damianbubak92/bramka-setup/Shared/KiCadLib/3dmodels/KEY-SMD_4P-L6.0-W6.0-P4.50-LS10.0.step

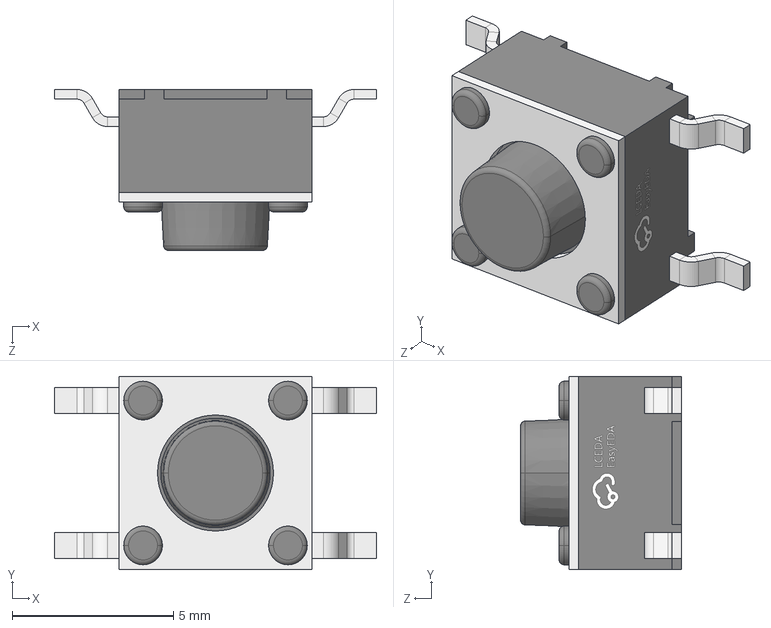
[picture p16: CAD file, 2026-07-04]
Shared/KiCadLib/3dmodels/KEY-SMD_4P-L6.0-W6.0-P4.50-LS10.0.step
10.0 x 6.00 x 5.00 mm
