damianbubak92/bramka-setup/Shared/KiCadLib/3dmodels/WSON-10_L2.5-W2.5-W0.50-TL-EP.step

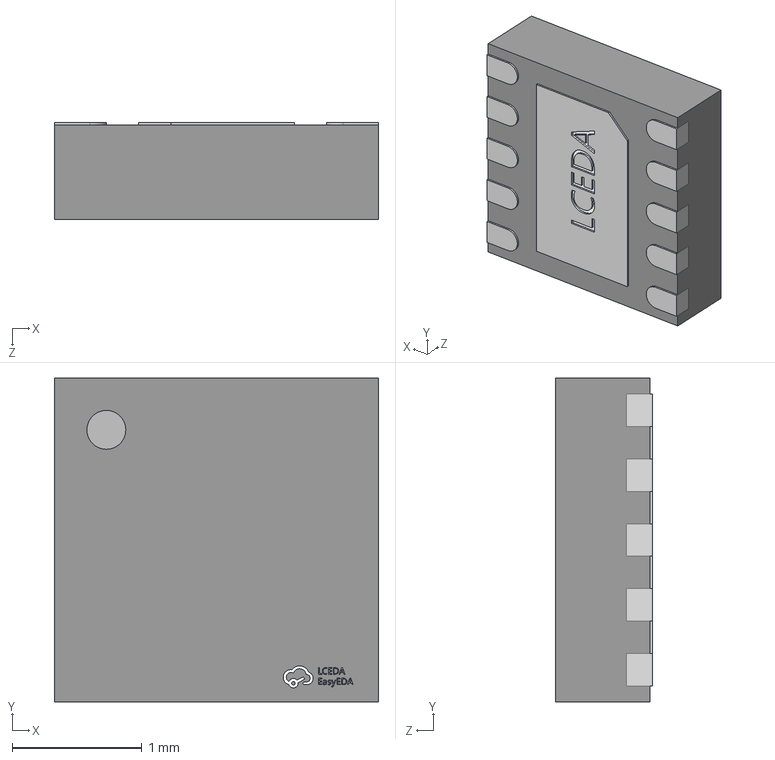
[picture p17: CAD file, 2026-07-04]
Shared/KiCadLib/3dmodels/WSON-10_L2.5-W2.5-W0.50-TL-EP.step
2.50 x 2.50 x 0.751 mm
