damianbubak92/bramka-setup/Shared/KiCadLib/3dmodels/SOT-23-6_L2.9-W1.6-H1.5-LS2.8-P0.95.step

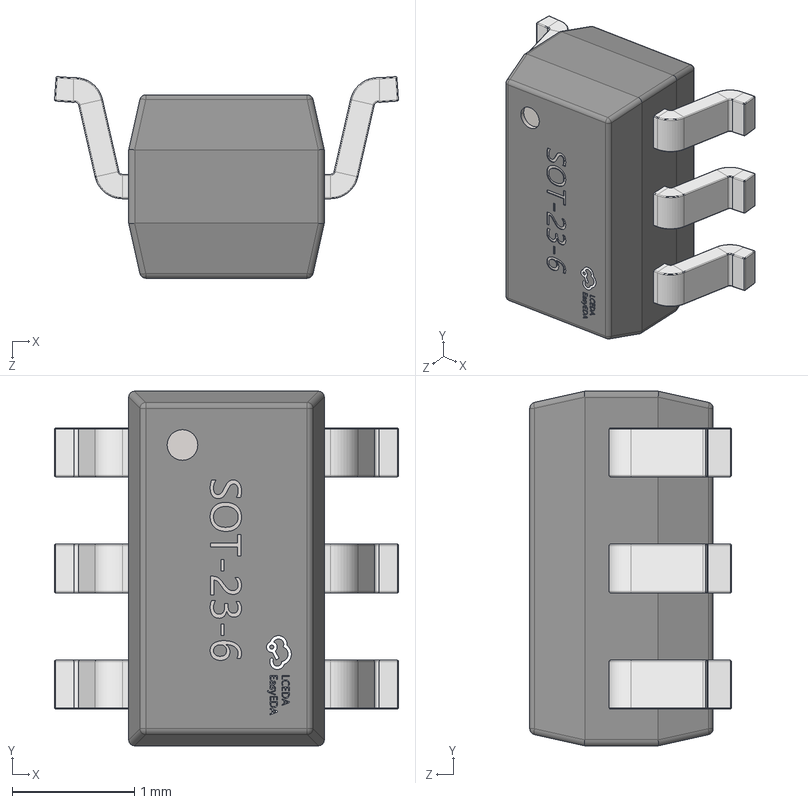
[picture p18: CAD file, 2026-07-04]
Shared/KiCadLib/3dmodels/SOT-23-6_L2.9-W1.6-H1.5-LS2.8-P0.95.step
2.81 x 2.90 x 1.65 mm
