damianbubak92/bramka-setup/Shared/KiCadLib/3dmodels/DFN-8_L2.5-W2.5-H1.0-P0.50.step

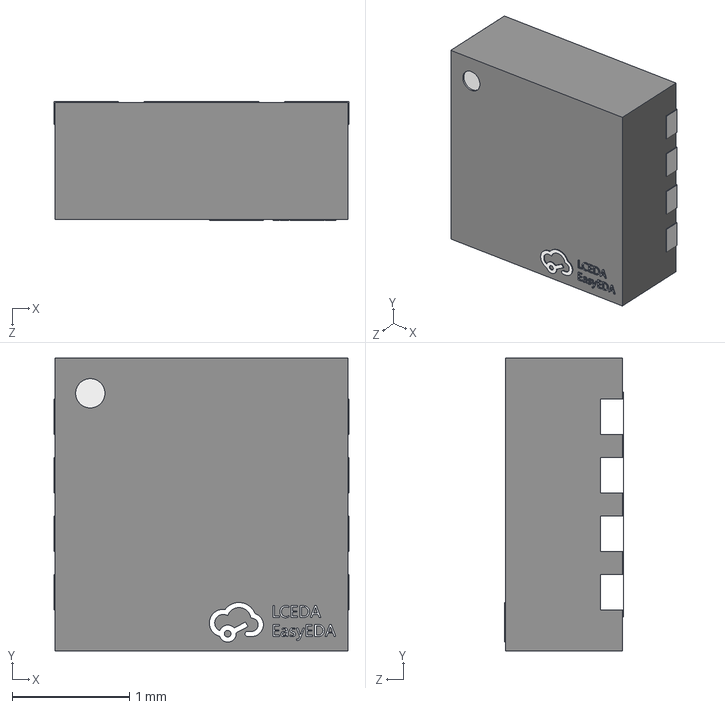
[picture p19: CAD file, 2026-07-03]
Shared/KiCadLib/3dmodels/DFN-8_L2.5-W2.5-H1.0-P0.50.step
2.52 x 2.50 x 1.02 mm
