damianbubak92/bramka-setup/Shared/KiCadLib/3dmodels/CC1310F128RGZR.step

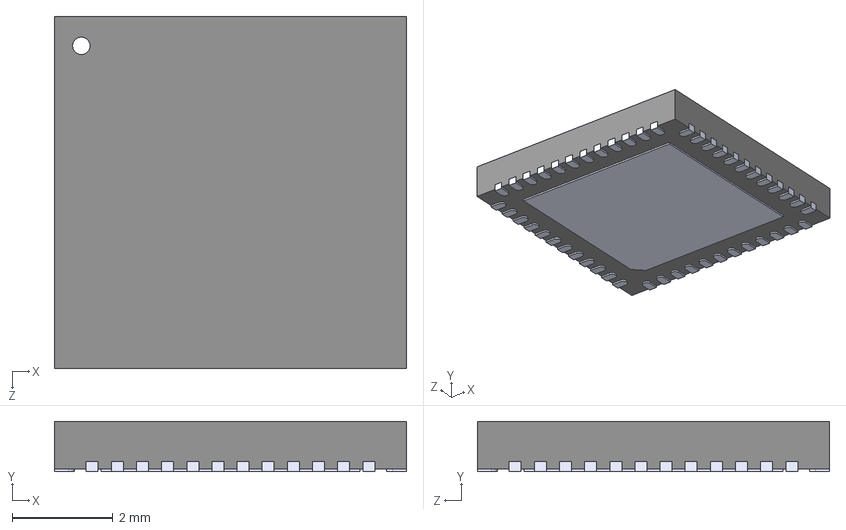
[picture p20: CAD file, 2026-07-03]
Shared/KiCadLib/3dmodels/CC1310F128RGZR.step
7.00 x 1.00 x 7.00 mm
