damianbubak92/bramka-setup/Shared/KiCadLib/3dmodels/DFN-10_L3.0-W3.0-H0.9-P0.50.step

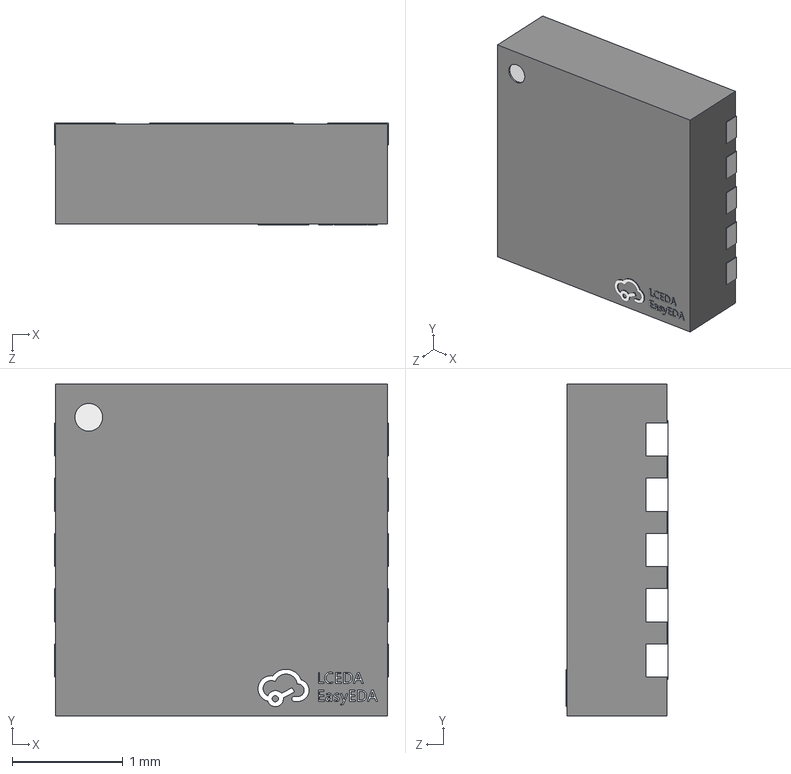
[picture p21: CAD file, 2026-07-03]
Shared/KiCadLib/3dmodels/DFN-10_L3.0-W3.0-H0.9-P0.50.step
3.02 x 3.00 x 0.92 mm
