damianbubak92/bramka-setup/Shared/KiCadLib/3dmodels/USB-C-SMD_TYPE-C-6PIN-2MD-073.step

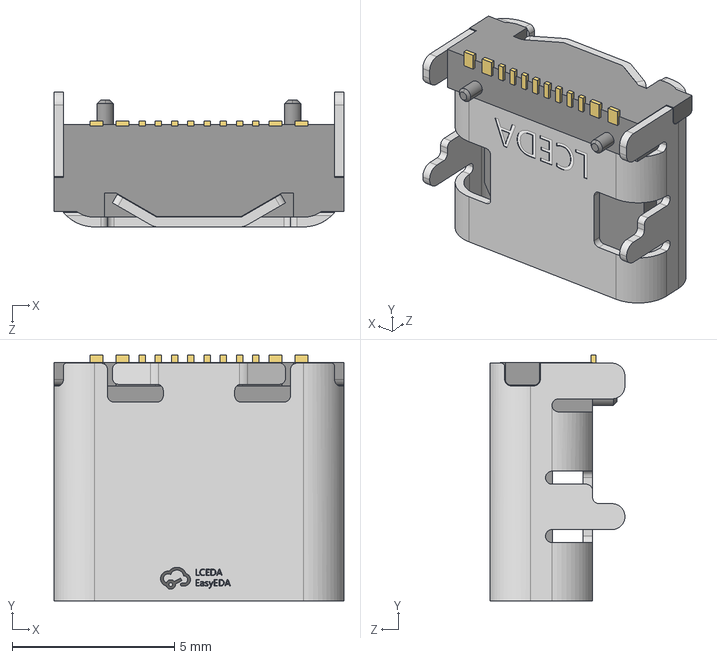
[picture p22: CAD file, 2026-07-03]
Shared/KiCadLib/3dmodels/USB-C-SMD_TYPE-C-6PIN-2MD-073.step
8.94 x 7.58 x 4.16 mm
