damianbubak92/bramka-setup/Nodes/LightSwitchNode/Firmware/scif.c

/// \addtogroup module_scif_driver_setup
//@{
#include "scif.h"
#include "scif_framework.h"
#include <ti/devices/DeviceFamily.h>
#include DeviceFamily_constructPath(inc/hw_types.h)
#include DeviceFamily_constructPath(inc/hw_memmap.h)
#include DeviceFamily_constructPath(inc/hw_aon_event.h)
#include DeviceFamily_constructPath(inc/hw_aon_rtc.h)
#include DeviceFamily_constructPath(inc/hw_aon_pmctl.h)
#include DeviceFamily_constructPath(inc/hw_aux_sce.h)
#include DeviceFamily_constructPath(inc/hw_aux_smph.h)
#include DeviceFamily_constructPath(inc/hw_aux_spim.h)
#include DeviceFamily_constructPath(inc/hw_aux_evctl.h)
#include DeviceFamily_constructPath(inc/hw_aux_aiodio.h)
#include DeviceFamily_constructPath(inc/hw_aux_timer01.h)
#include DeviceFamily_constructPath(inc/hw_aux_sysif.h)
#include DeviceFamily_constructPath(inc/hw_event.h)
#include DeviceFamily_constructPath(inc/hw_ints.h)
#include DeviceFamily_constructPath(inc/hw_ioc.h)
#include <string.h>
#if defined(__IAR_SYSTEMS_ICC__)
    #include <intrinsics.h>
#endif


// OSAL function prototypes
uint32_t scifOsalEnterCriticalSection(void);
void scifOsalLeaveCriticalSection(uint32_t key);




/// Firmware image to be uploaded to the AUX RAM
static const uint16_t pAuxRamImage[] = {
    /*0x0000*/ 0x140E, 0x0417, 0x140E, 0x0440, 0x140E, 0x044A, 0x140E, 0x0467, 0x140E, 0x0470, 0x140E, 0x0479, 0x140E, 0x0482, 0x8953, 0x9954, 
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
    /*0x03C0*/ 0x9D1E, 0xDDA9, 0x9D25, 0x9DA9, 0x50F1, 0x9F3D, 0x191C, 0x9A08, 0xA60D, 0x1103, 0x9F19, 0x9801, 0x5103, 0x9F3D, 0x10ED, 0xCF39, 
    /*0x03E0*/ 0x9D44, 0xCDAD, 0x9D24, 0x40EF, 0x9F3C, 0x0677, 0x10ED, 0x9F19, 0x50EF, 0xDF1D, 0x6117, 0xEF1E, 0xEA00, 0xBE1F, 0x60F1, 0xEF1E, 
    /*0x0400*/ 0x7103, 0xFF1F, 0xFA60, 0x9E18, 0xED29, 0xA607, 0xFD41, 0xFDA1, 0xFD19, 0xFD26, 0x9D47, 0x9DA9, 0x0615, 0xFD41, 0xFDA1, 0x9DAA, 
    /*0x0420*/ 0xFD19, 0xEDAA, 0xFD26, 0x9D47, 0x9DA9, 0x60ED, 0x9F3E, 0x6103, 0xEF1E, 0xE8E0, 0x7103, 0xEF3F, 0x0626, 0xED45, 0xEDA1, 0xDDAB, 
    /*0x0440*/ 0xED1D, 0xDD44, 0xDDAB, 0xED25, 0xDD46, 0xDDA9, 0x68BF, 0xE802, 0x9F3E, 0xED41, 0xFD41, 0xFDAD, 0xED27, 0xDD2E, 0xA601, 0xDD46, 
    /*0x0460*/ 0xED41, 0xFD41, 0xFDAA, 0xED27, 0xDD2E, 0x9E01, 0xDD46, 0x60EF, 0xDF3E, 0x68BF, 0xE804, 0xDF3E, 0x5117, 0xDF1D, 0xDA00, 0xB602, 
    /*0x0480*/ 0x9806, 0x0643, 0x980C, 0x58BF, 0xD80A, 0x9F3D, 0xCD29, 0x9E17, 0x1001, 0x5000, 0x6103, 0xDF3E, 0x58BA, 0x5D1B, 0x5119, 0xDF1D, 
    /*0x04A0*/ 0xD801, 0x6119, 0xDF3E, 0x5119, 0xDF1D, 0x8605, 0xDADC, 0x9E06, 0x10ED, 0xCF39, 0x1000, 0x4119, 0x9F3C, 0x1000, 0x0668, 0x1000, 
    /*0x04C0*/ 0x4103, 0xCF1C, 0xC801, 0x5103, 0xCF3D, 0x4000, 0x5119, 0xCF3D, 0x4117, 0xCF1C, 0x9D2C, 0xB605, 0x4117, 0x9F3C, 0x4001, 0x4CEC, 
    /*0x04E0*/ 0x0674, 0x48EC, 0xCD09, 0x4CEC, 0x48BF, 0xC80C, 0x9F3C, 0xA808, 0xB808, 0x8801, 0x8A02, 0xA601, 0x054F, 0x171A, 0x70FF, 0xFBA4, 
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
};


/// Look-up table that converts from AUX I/O index to MCU IOCFG offset
static const uint8_t pAuxIoIndexToMcuIocfgOffsetLut[] = {
    0, 68, 64, 60, 56, 52, 48, 44, 40, 36, 32, 28, 24, 20, 16, 12, 8, 4, 0, 120, 116, 112, 108, 104, 100, 96, 92, 88, 84, 80, 76, 72
};


/** \brief Look-up table of data structure information for each task
  *
  * There is one entry per data structure (\c cfg, \c input, \c output and \c state) per task:
  * - [31:20] Data structure size (number of 16-bit words)
  * - [19:12] Buffer count (when 2+, first data structure is preceded by buffering control variables)
  * - [11:0] Address of the first data structure
  */
static const uint32_t pScifTaskDataStructInfoLut[] = {
//  cfg         input       output      state       
    0x00501170, 0x00000000, 0x00E03180, 0x033011D4  // Capacitive Touch
};




/// Run-time logging signatures (CRC-16) for each data structure for each task
static const uint16_t pRtlTaskStructSignatures[] = {
    0x4E21, 0x0000, 0xD840, 0x4C51
};




// No task-specific initialization functions




// No task-specific uninitialization functions




/** \brief Performs driver setup dependent hardware initialization
  *
  * This function is called by the internal driver initialization function, \ref scifInit().
  */
static void scifDriverSetupInit(void) {

    // Select SCE clock frequency in active mode
    HWREG(AON_PMCTL_BASE + AON_PMCTL_O_AUXSCECLK) = AON_PMCTL_AUXSCECLK_SRC_SCLK_HFDIV2;

    // Set the default power mode
    scifSetSceOpmode(AUX_SYSIF_OPMODEREQ_REQ_A);

    // Initialize task resource dependencies
    scifInitIo(22, AUXIOMODE_OPEN_DRAIN | (0 << BI_AUXIOMODE_OUTPUT_DRIVE_STRENGTH), -1, 1);
    scifInitIo(20, AUXIOMODE_OPEN_DRAIN | (0 << BI_AUXIOMODE_OUTPUT_DRIVE_STRENGTH), -1, 1);
    scifInitIo(25, AUXIOMODE_OPEN_SOURCE | (0 << BI_AUXIOMODE_OUTPUT_DRIVE_STRENGTH), -1, 0);
    HWREG(AON_PMCTL_BASE + AON_PMCTL_O_AUXSCECLK) = (HWREG(AON_PMCTL_BASE + AON_PMCTL_O_AUXSCECLK) & (~AON_PMCTL_AUXSCECLK_PD_SRC_M)) | AON_PMCTL_AUXSCECLK_PD_SRC_SCLK_LF;
    HWREG(AON_RTC_BASE + AON_RTC_O_CTL) |= AON_RTC_CTL_RTC_4KHZ_EN;

} // scifDriverSetupInit




/** \brief Performs driver setup dependent hardware uninitialization
  *
  * This function is called by the internal driver uninitialization function, \ref scifUninit().
  */
static void scifDriverSetupUninit(void) {

    // Uninitialize task resource dependencies
    scifUninitIo(22, -1);
    scifUninitIo(20, -1);
    scifUninitIo(25, -1);
    HWREG(AON_PMCTL_BASE + AON_PMCTL_O_AUXSCECLK) = (HWREG(AON_PMCTL_BASE + AON_PMCTL_O_AUXSCECLK) & (~AON_PMCTL_AUXSCECLK_PD_SRC_M)) | AON_PMCTL_AUXSCECLK_PD_SRC_NO_CLOCK;
    HWREG(AON_RTC_BASE + AON_RTC_O_CTL) &= ~AON_RTC_CTL_RTC_4KHZ_EN;

} // scifDriverSetupUninit




/** \brief Re-initializes I/O pins used by the specified tasks
  *
  * It is possible to stop a Sensor Controller task and let the System CPU borrow and operate its I/O
  * pins. For example, the Sensor Controller can operate an SPI interface in one application state while
  * the System CPU with SSI operates the SPI interface in another application state.
  *
  * This function must be called before \ref scifExecuteTasksOnceNbl() or \ref scifStartTasksNbl() if
  * I/O pins belonging to Sensor Controller tasks have been borrowed System CPU peripherals.
  *
  * \param[in]      bvTaskIds
  *     Bit-vector of task IDs for the task I/Os to be re-initialized
  */
void scifReinitTaskIo(uint32_t bvTaskIds) {
    if (bvTaskIds & (1 << SCIF_CAPACITIVE_TOUCH_TASK_ID)) {
        scifReinitIo(22, -1, 0);
        scifReinitIo(20, -1, 0);
        scifReinitIo(25, -1, 0);
    }
} // scifReinitTaskIo




/// Driver setup data, to be used in the call to \ref scifInit()
const SCIF_DATA_T scifDriverSetup = {
    (volatile SCIF_INT_DATA_T*) 0x400E0158,
    (volatile SCIF_TASK_CTRL_T*) 0x400E0166,
    (volatile uint16_t*) 0x400E014C,
    0x0000,
    sizeof(pAuxRamImage),
    pAuxRamImage,
    pScifTaskDataStructInfoLut,
    pAuxIoIndexToMcuIocfgOffsetLut,
    0x0000,
    24,
    scifDriverSetupInit,
    scifDriverSetupUninit,
    (volatile uint16_t*) 0x400E0154,
    (volatile uint16_t*) 0x400E0156,
    pRtlTaskStructSignatures
};




// No task-specific API available


//@}


// Generated by DESKTOP-S5PV63S at 2026-08-21 01:49:11.021
