damianbubak92/bramka-setup/Nodes/TempHumNode/Firmware/radio.c

/*
 * radio.c - one-shot blocking RF send for the power-cycled T&H node.
 * Reuses the proven gen2 PHY (smartrf_settings) + frame format so the existing
 * gen2 gateway receives it unchanged. TX is chained to a short RX window to catch
 * the gateway ACK; retried a few times. No tasks/events - linear, then RF_close.
 */
#include "radio.h"

#include <string.h>
#include <ti/drivers/rf/RF.h>
#include <ti/devices/DeviceFamily.h>
#include DeviceFamily_constructPath(driverlib/rf_prop_mailbox.h)

#include "smartrf_settings/smartrf_settings.h"
#include "RFQueue.h"

#define MAX_RETRIES         3
#define PAYLOAD_LENGTH      64   /* headroom for 'E' frames (factory_id[8]) + JOIN_ACCEPT */
#define NUM_DATA_ENTRIES    2
#define NUM_APPENDED_BYTES  2
/* RF core runs at 4 MHz -> 4 ticks/us. ACK window after TX. */
#define ACK_WINDOW_US       50000
#define ACK_WINDOW_TICKS    (ACK_WINDOW_US * 4)

static RF_Object rfObject;
static RF_Handle rfHandle;

#pragma DATA_ALIGN(rxDataEntryBuffer, 4)
static uint8_t rxDataEntryBuffer[RF_QUEUE_DATA_ENTRY_BUFFER_SIZE(
        NUM_DATA_ENTRIES, PAYLOAD_LENGTH, NUM_APPENDED_BYTES)];
static dataQueue_t dataQueue;
static rfc_dataEntryGeneral_t *currentDataEntry;
static rfc_propRxOutput_t rxStatistics;

static uint8_t txSeq = 0;

static uint8_t calcChecksum(const uint8_t *d, uint8_t len)
{
    uint8_t crc = 0, i;
    for (i = 0; i < len; i++) crc ^= d[i];
    return crc;
}

bool radio_send_message(const MessageStruct *msg, uint8_t destAddr,
                        const uint8_t *factoryId, uint8_t *nackCmd)
{
    RF_Params rfParams;
    RF_Params_init(&rfParams);

    if (RFQueue_defineQueue(&dataQueue, rxDataEntryBuffer, sizeof(rxDataEntryBuffer),
                            NUM_DATA_ENTRIES, PAYLOAD_LENGTH + NUM_APPENDED_BYTES)) {
        return false;
    }

    /* RX (ACK window), chained after TX */
    RF_cmdPropRx.pQueue = &dataQueue;
    RF_cmdPropRx.rxConf.bAutoFlushIgnored = 1;
    RF_cmdPropRx.rxConf.bAutoFlushCrcErr  = 1;
    RF_cmdPropRx.maxPktLen = PAYLOAD_LENGTH;
    RF_cmdPropRx.pktConf.bRepeatOk  = 0;
    RF_cmdPropRx.pktConf.bRepeatNok = 0;
    RF_cmdPropRx.pOutput = (uint8_t *)&rxStatistics;
    RF_cmdPropRx.endTrigger.triggerType = TRIG_REL_PREVEND;
    RF_cmdPropRx.endTime = ACK_WINDOW_TICKS;

    RF_cmdPropTx.startTrigger.triggerType = TRIG_NOW;
    RF_cmdPropTx.startTrigger.pastTrig    = 1;
    RF_cmdPropTx.pNextOp   = (rfc_radioOp_t *)&RF_cmdPropRx;
    RF_cmdPropTx.condition.rule = COND_STOP_ON_FALSE;  /* RX only if TX ok */

    rfHandle = RF_open(&rfObject, &RF_prop, (RF_RadioSetup *)&RF_cmdPropRadioDivSetup, &rfParams);
    if (rfHandle == NULL) return false;
    RF_runCmd(rfHandle, (RF_Op *)&RF_cmdFs, RF_PriorityNormal, NULL, 0);

    /* Build frame: 'E' [dest]['E'][src][factory_id:8][msg][seq][crc8] when a chip id is
     * given (telemetry/confirm - lets the gateway key its §14 pending-command table),
     * else legacy 'D' [dest]['D'][src][msg][seq][crc8] (JOIN). The CRC covers src..seq
     * (calcChecksum(&frame[2], hdr+len-1)) exactly as the gateway validates it. */
    uint8_t frame[3 + NODE_FACTORY_ID_LEN + sizeof(MessageStruct) + 2];
    uint8_t len = msg->length;
    uint8_t hdr;
    frame[0] = destAddr;
    frame[2] = msg->id;
    if (factoryId != NULL) {
        frame[1] = 'E';
        memcpy(&frame[3], factoryId, NODE_FACTORY_ID_LEN);
        memcpy(&frame[3 + NODE_FACTORY_ID_LEN], msg, len);
        hdr = (uint8_t)(3 + NODE_FACTORY_ID_LEN);
    } else {
        frame[1] = 'D';
        memcpy(&frame[3], msg, len);
        hdr = 3;
    }
    txSeq++;
    frame[hdr + len]     = txSeq;
    frame[hdr + len + 1] = calcChecksum(&frame[2], (uint8_t)(hdr + len - 1));
    uint8_t expectedCRC  = frame[hdr + len + 1];
    uint8_t pktLen       = (uint8_t)(hdr + len + 2);

    if (nackCmd != NULL) { *nackCmd = 0u; }

    /* A reply ends the retry loop, whether ACK or NACK (both mean the gateway heard us).
     * NACK carries a pending CMD_* in byte [3] (§14) - hand it to the caller. */
    bool gotReply = false;
    int retry;
    for (retry = 0; retry <= MAX_RETRIES && !gotReply; retry++) {
        RF_cmdPropTx.pPkt   = frame;
        RF_cmdPropTx.pktLen = pktLen;
        /* Blocks through TX and the chained RX (ACK/NACK) window. */
        RF_runCmd(rfHandle, (RF_Op *)&RF_cmdPropTx, RF_PriorityNormal, NULL, 0);

        currentDataEntry = RFQueue_getDataEntry();
        while (currentDataEntry->status == DATA_ENTRY_FINISHED) {
            uint8_t  plen  = *(uint8_t *)(&currentDataEntry->data);
            uint8_t *pdata = (uint8_t *)(&currentDataEntry->data) + 1;
            /* Reply to our uplink: [our addr][tag][dest we used][crc-or-cmd] */
            if (plen >= 4 && pdata[0] == msg->id && pdata[2] == destAddr) {
                if (pdata[1] == RF_REPLY_ACK && pdata[3] == expectedCRC) {
                    gotReply = true;                            /* normal ACK */
                } else if (pdata[1] == RF_REPLY_NACK) {
                    if (nackCmd != NULL) { *nackCmd = pdata[3]; }  /* NACK carries a pending CMD_* */
                    gotReply = true;
                }
            }
            RFQueue_nextEntry();
            currentDataEntry = RFQueue_getDataEntry();
        }
    }

    RF_close(rfHandle);
    return gotReply;
}

/* Listen for the gateway's JOIN_ACCEPT (arrives after the user approves on the phone,
 * so we poll RX in ~500 ms windows up to timeoutMs). Frame parsing mirrors the gen2
 * node rfEchoTx RX: [dest][tag][src][ ('E': factory_id[8]) MessageStruct ][seq][crc8].
 * For JOIN_ACCEPT the gateway addresses the unprovisioned node (dest = 0xFF) and, on an
 * 'E' frame, targets this chip via the frame-level factory_id. */
bool radio_wait_join_accept(const uint8_t *factoryId, uint8_t *assignedAddr, uint32_t timeoutMs)
{
    RF_Params rfParams;
    RF_Params_init(&rfParams);

    if (RFQueue_defineQueue(&dataQueue, rxDataEntryBuffer, sizeof(rxDataEntryBuffer),
                            NUM_DATA_ENTRIES, PAYLOAD_LENGTH + NUM_APPENDED_BYTES)) {
        return false;
    }

    /* Standalone RX: one packet or a ~500 ms window, then we drain + retry. */
    RF_cmdPropRx.pQueue = &dataQueue;
    RF_cmdPropRx.rxConf.bAutoFlushIgnored = 1;
    RF_cmdPropRx.rxConf.bAutoFlushCrcErr  = 1;
    RF_cmdPropRx.maxPktLen = PAYLOAD_LENGTH;
    RF_cmdPropRx.pktConf.bRepeatOk  = 0;   /* end after 1 good packet */
    RF_cmdPropRx.pktConf.bRepeatNok = 0;
    RF_cmdPropRx.pOutput = (uint8_t *)&rxStatistics;
    RF_cmdPropRx.pNextOp = NULL;
    RF_cmdPropRx.startTrigger.triggerType = TRIG_NOW;
    RF_cmdPropRx.startTrigger.pastTrig    = 1;
    RF_cmdPropRx.endTrigger.triggerType   = TRIG_REL_START;
    RF_cmdPropRx.endTime = 500 * 4000;     /* 500 ms @ 4 MHz */

    rfHandle = RF_open(&rfObject, &RF_prop, (RF_RadioSetup *)&RF_cmdPropRadioDivSetup, &rfParams);
    if (rfHandle == NULL) return false;
    RF_runCmd(rfHandle, (RF_Op *)&RF_cmdFs, RF_PriorityNormal, NULL, 0);

    bool got = false;
    uint32_t elapsed = 0;
    while (!got && elapsed < timeoutMs) {
        RF_runCmd(rfHandle, (RF_Op *)&RF_cmdPropRx, RF_PriorityNormal, NULL, 0);
        elapsed += 500;

        currentDataEntry = RFQueue_getDataEntry();
        while (!got && currentDataEntry->status == DATA_ENTRY_FINISHED) {
            uint8_t  plen = *(uint8_t *)(&currentDataEntry->data);
            uint8_t *p    = (uint8_t *)(&currentDataEntry->data) + 1;

            /* addressed to us (unprovisioned = 0xFF) and CRC ok */
            if (plen >= 5 && p[0] == ADDR_UNPROVISIONED &&
                p[plen - 1] == calcChecksum(&p[2], (uint8_t)(plen - 3))) {

                uint8_t tag  = p[1];
                int     mOff = -1;
                if (tag == 'E' && plen >= 13 &&
                    memcmp(&p[3], factoryId, NODE_FACTORY_ID_LEN) == 0) {
                    mOff = 11;                 /* skip [dest][tag][src][factory_id:8] */
                } else if (tag == 'D') {
                    mOff = 3;                  /* skip [dest][tag][src] */
                }

                if (mOff >= 0) {
                    MessageStruct m;
                    memset(&m, 0, sizeof(m));
                    int mlen = (int)plen - mOff - 2;   /* minus [seq][crc] */
                    if (mlen > (int)sizeof(m)) mlen = (int)sizeof(m);
                    if (mlen > 0) memcpy(&m, &p[mOff], (size_t)mlen);

                    if (m.cmd == CMD_JOIN_ACCEPT) {
                        *assignedAddr = m.payload.joinAcceptData.assigned_addr;

                        /* ACK the gateway: [gw src]['A'][our dest][echoed crc] */
                        uint8_t ack[4];
                        ack[0] = p[2];
                        ack[1] = 'A';
                        ack[2] = p[0];
                        ack[3] = p[plen - 1];
                        RF_cmdPropTx.pPkt   = ack;
                        RF_cmdPropTx.pktLen = 4;
                        RF_cmdPropTx.pNextOp = NULL;
                        RF_cmdPropTx.condition.rule = COND_NEVER;
                        RF_cmdPropTx.startTrigger.triggerType = TRIG_NOW;
                        RF_cmdPropTx.startTrigger.pastTrig    = 1;
                        RF_runCmd(rfHandle, (RF_Op *)&RF_cmdPropTx, RF_PriorityNormal, NULL, 0);

                        got = true;
                    }
                }
            }
            RFQueue_nextEntry();
            currentDataEntry = RFQueue_getDataEntry();
        }
    }

    RF_close(rfHandle);
    return got;
}
