damianbubak92/bramka-setup/Gateway/Firmware/M4F/engine.c

/**
 * engine.c - Automation engine core (M4F). Ported ~1:1 from gen1
 * (automationRules.c + coreTask.c folding). RTOS-agnostic - see engine.h.
 */
#include "engine.h"
#include <string.h>

/* ========================================================================= *
 * STATE
 * ========================================================================= */

/* PER-NODE live state, keyed by RF address (0x10-0xEF). gen2 multi-node: each node
 * has its own record, so two nodes of the SAME type (e.g. gen1 solar 0xF1 + a gen2
 * solar) no longer overwrite each other. Rules reference a node by address (Go
 * resolves node_id -> address at push). `inUse` = the node has reported at least once;
 * a condition on a node that hasn't reported yet is fail-safe (treated as not met),
 * so rules never fire on absent/stale data. Direct-indexed by address for O(1); ~12 KB,
 * placed in DDR alongside g_rules (same section). */
typedef struct {
    uint8_t inUse;
    uint8_t type;       /* NODE_* */
    union {             /* only the node's own type's fields (saves ~1/4 the RAM) */
        struct {
            float   T1, T2, T3, T4, Tcol;
            int32_t energyGain, flowRate;
            uint8_t pumpState;
        } solar;
        struct {
            float sBuforTemp;
        } bufor;
        struct {
            float    temperature, humidity;
            uint16_t batt_mv;
        } th;
    } d;
} NodeRec;   /* 36 B; x256 = 9 KB in DDR (fits alongside g_rules in .bss.engine_rules) */

static NodeRec g_node[256]
    __attribute__((section(".bss.engine_rules")));  /* DDR (see g_rules note) */

/* Vestigial: engine_get_state()/MSG_NODE_STATE is no longer sent (Go reads telemetry
 * from the raw NODE_TELEMETRY path -> DB). Kept zeroed so the .h symbol still links. */
static const NodesData g_state_stub = { 0 };

static EngineActionFn g_action_fn  = NULL;
static void          *g_action_ctx = NULL;
static EngineClockFn  g_clock_fn   = NULL;

/* Wall clock for COND_TIME. M4F has no RTC: the platform injects a monotonic
 * microsecond clock (g_clock_fn) and a wall time (engine_set_time). The engine
 * advances the wall time by the monotonic delta, so COND_TIME stays accurate
 * between syncs and the minute tick can align to :00. */
static struct {
    uint32_t base_secs;   /* seconds-of-day at last sync (0..86399) */
    uint64_t anchor_us;   /* g_clock_fn() at last sync */
    bool     valid;
} g_wall = { 0, 0, false };

/* Double-buffered ruleset. g_active selects the live set; the other is the
 * shadow under construction. Swapping g_active is the atomic commit.
 *
 * This is large (2 * MAX_RULES * sizeof(AutomationRule) ~= 39 KB at MAX_RULES
 * =100). The M4F internal DRAM is only 64 KB, so it is placed in a dedicated
 * section the linker maps to DDR (see linker.cmd: .bss.engine_rules > M4F_DDR,
 * and docs/ENGINE-INTEGRATION.md). Uninitialized/NOLOAD is fine: rules are
 * written before activation and g_count starts at 0, so no slot is read until a
 * successful commit has filled it. (The section attribute is ignored by host
 * compilers if engine.c is ever built off-target.) */
static AutomationRule g_rules[2][MAX_RULES]
    __attribute__((section(".bss.engine_rules")));
static uint16_t       g_count[2]  = { 0, 0 };
static volatile uint8_t g_active  = 0;

/* TIME-rule fire dedup: the wall-minute (hour*60+minute) we last evaluated TIME
 * rules for. The minute tick is meant to run once per minute; this guarantees it
 * even if EVAL_TIME gets triggered more than once in the same wall-minute (e.g. a
 * scheduling quirk or a lingering wake), so TIME rules fire at most once per
 * minute. -1 = none yet. Node-data (EVAL_NODE) rules are unaffected. */
static int g_last_time_min = -1;

/* Shadow-build state */
static bool     g_building       = false;
static uint8_t  g_shadow         = 1;     /* index being filled (= !g_active) */
static uint16_t g_shadow_expected = 0;
static uint16_t g_shadow_filled   = 0;

/* ========================================================================= *
 * CRC32 (IEEE, poly 0xEDB88320) - matches Go hash/crc32 (ChecksumIEEE).
 * crc32 of zero bytes == 0x00000000.
 * ========================================================================= */
static uint32_t crc32_calc(const uint8_t *data, size_t len)
{
    uint32_t crc = 0xFFFFFFFFu;
    size_t i;
    int b;

    for (i = 0; i < len; i++) {
        crc ^= data[i];
        for (b = 0; b < 8; b++) {
            uint32_t mask = (uint32_t)(-(int32_t)(crc & 1u));
            crc = (crc >> 1) ^ (0xEDB88320u & mask);
        }
    }
    return crc ^ 0xFFFFFFFFu;
}

/* ========================================================================= *
 * LIFECYCLE
 * ========================================================================= */
void engine_init(EngineActionFn action_fn, void *action_ctx,
                 EngineClockFn clock_fn)
{
    g_action_fn  = action_fn;
    g_action_ctx = action_ctx;
    g_clock_fn   = clock_fn;
    g_wall.valid = false;
    g_last_time_min = -1;

    g_active = 0;
    g_count[0] = 0;
    g_count[1] = 0;
    g_building = false;
    g_shadow_expected = 0;
    g_shadow_filled = 0;
}

/* ========================================================================= *
 * LIVE STATE - gen1 coreTask folding, ported
 * ========================================================================= */
bool engine_update_node(const MessageStruct *msg)
{
    if (msg == NULL) {
        return false;
    }
    NodeRec *nd = &g_node[msg->id];   /* per-node record, keyed by RF address */

    if (msg->type == NODE_SOLAR_CONTROLLER && msg->cmd == CMD_SEND_DATA_TO_DB) {
        nd->type            = NODE_SOLAR_CONTROLLER;
        nd->d.solar.T4         = msg->payload.solarData.T4;
        nd->d.solar.T3         = msg->payload.solarData.T3;
        nd->d.solar.T2         = msg->payload.solarData.T2;
        nd->d.solar.T1         = msg->payload.solarData.T1;
        nd->d.solar.Tcol       = msg->payload.solarData.Tcol;
        nd->d.solar.energyGain = msg->payload.solarData.energyGain;
        nd->d.solar.flowRate   = msg->payload.solarData.flowRate;
        nd->d.solar.pumpState  = msg->payload.solarData.pumpState;
        nd->inUse           = 1u;
        return true;
    }
    if (msg->type == NODE_SOLAR_CONTROLLER && msg->cmd == CMD_SEND_PUMP_STATUS) {
        nd->type              = NODE_SOLAR_CONTROLLER;
        nd->d.solar.pumpState = msg->payload.pumpData.pumpState;
        nd->inUse             = 1u;
        return true;
    }
    if (msg->type == NODE_BUFOR_CONTROLLER) {
        nd->type             = NODE_BUFOR_CONTROLLER;
        nd->d.bufor.sBuforTemp = msg->payload.buforData.sBuforTemp;
        nd->inUse            = 1u;
        return true;
    }
    if (msg->type == NODE_TH_SENSOR) {
        nd->type           = NODE_TH_SENSOR;
        nd->d.th.temperature = msg->payload.thData.temperature;
        nd->d.th.humidity    = msg->payload.thData.humidity;
        nd->d.th.batt_mv     = msg->payload.thData.batt_mv;
        nd->inUse          = 1u;
        return true;
    }
    return false;
}

const NodesData *engine_get_state(void)
{
    return &g_state_stub;  /* vestigial - see g_state_stub note */
}

/* Current wall time, advancing the last sync by the monotonic delta.
 * Returns false if no valid time / no clock source (TIME conds fail-safe off). */
static bool wall_now(uint8_t *hour, uint8_t *minute, uint8_t *second)
{
    uint64_t now, elapsed_s;
    uint32_t secs;

    if (!g_wall.valid || g_clock_fn == NULL) {
        return false;
    }
    now = g_clock_fn();
    elapsed_s = (now - g_wall.anchor_us) / 1000000ULL;
    secs = (uint32_t)(((uint64_t)g_wall.base_secs + elapsed_s) % 86400ULL);
    if (hour)   *hour   = (uint8_t)(secs / 3600u);
    if (minute) *minute = (uint8_t)((secs / 60u) % 60u);
    if (second) *second = (uint8_t)(secs % 60u);
    return true;
}

void engine_set_time(uint8_t hour, uint8_t minute, uint8_t second)
{
    g_wall.base_secs = (uint32_t)hour * 3600u + (uint32_t)minute * 60u + second;
    g_wall.anchor_us = (g_clock_fn != NULL) ? g_clock_fn() : 0u;
    g_wall.valid     = true;
}

void engine_clear_time(void)
{
    g_wall.valid = false;
}

uint32_t engine_ms_to_next_minute(void)
{
    uint64_t now, wall_ms, into;

    if (!g_wall.valid || g_clock_fn == NULL) {
        return 60000u;  /* no clock: free-run a 60s period (TIME rules fail-safe off) */
    }
    now = g_clock_fn();
    /* Wall time in ms, advanced from the last sync. Only the within-minute
     * remainder matters, computed at full ms resolution so the wake lands on
     * :00 regardless of sub-second phase (no integer-second flooring jitter). */
    wall_ms = (uint64_t)g_wall.base_secs * 1000ull + (now - g_wall.anchor_us) / 1000ull;
    into = wall_ms % 60000ull;            /* ms elapsed into the current minute */
    return (uint32_t)(60000ull - into);   /* 1..60000 ms to the next :00 */
}

/* ========================================================================= *
 * EVALUATOR - port of gen1 evaluateAutomationRules()
 * ========================================================================= */

/* Read one parameter of the node at `addr` from its per-node record. The app offers
 * only params valid for the selected node's type, so a solar param on a solar node etc.
 * Absent/unknown -> 0 (callers gate on g_node[addr].inUse first, so this isn't reached
 * for a node that never reported). */
static float getNodeParam(uint8_t addr, uint8_t parameter)
{
    const NodeRec *nd = &g_node[addr];
    if (nd->type == NODE_SOLAR_CONTROLLER) {
        switch (parameter) {
            case PARAM_T1:          return nd->d.solar.T1;
            case PARAM_T2:          return nd->d.solar.T2;
            case PARAM_T3:          return nd->d.solar.T3;
            case PARAM_T4:          return nd->d.solar.T4;
            case PARAM_TCOL:        return nd->d.solar.Tcol;
            case PARAM_ENERGY_GAIN: return (float)nd->d.solar.energyGain;
            case PARAM_FLOW_RATE:   return (float)nd->d.solar.flowRate;
            case PARAM_PUMP_STATE:  return (float)nd->d.solar.pumpState;
            default:                return 0.0f;
        }
    }
    if (nd->type == NODE_BUFOR_CONTROLLER) {
        return (parameter == PARAM_SBUF_TEMP) ? nd->d.bufor.sBuforTemp : 0.0f;
    }
    if (nd->type == NODE_TH_SENSOR) {
        switch (parameter) {
            case PARAM_TEMPERATURE: return nd->d.th.temperature;
            case PARAM_HUMIDITY:    return nd->d.th.humidity;
            case PARAM_BATT_MV:     return (float)nd->d.th.batt_mv;
            default:                return 0.0f;
        }
    }
    return 0.0f;  /* param not valid for this node's type */
}

/* Current wall time snapped to the minute boundary (+4s forward bias) - the same
 * notion of "tick minute" the EVAL_TIME dedup uses. Rules are authored in WHOLE
 * minutes, and a TIME tick can wake a few seconds before/after :00 (FreeRTOS-tick
 * vs ClockP skew, scheduling jitter). With +4s, anything from :56 onward reads as
 * the next minute, so e.g. 22:44:56..22:45:04 all evaluate as 22:45:00 - a rule
 * whose window starts at the boundary fires on the intended minute, never one late. */
#define WALL_TICK_BIAS_S  4u

static bool wall_now_rounded(uint8_t *hour, uint8_t *minute)
{
    uint8_t h, m, s;
    uint32_t total;

    if (!wall_now(&h, &m, &s)) {
        return false;
    }
    total = ((uint32_t)h * 3600u + (uint32_t)m * 60u + (uint32_t)s + WALL_TICK_BIAS_S) % 86400u;
    if (hour)   *hour   = (uint8_t)(total / 3600u);
    if (minute) *minute = (uint8_t)((total / 60u) % 60u);
    return true;
}

static bool evaluateTimeCondition(const TimeCondition *tc)
{
    uint8_t h, m;
    bool afterStart, beforeEnd;

    if (!wall_now_rounded(&h, &m)) {
        return false;  /* fail-safe: no clock => TIME never matches */
    }
    /* Range assumed not to cross midnight (gen1 behavior). */
    afterStart = (h > tc->hourStart) || (h == tc->hourStart && m >= tc->minStart);
    beforeEnd  = (h < tc->hourEnd)   || (h == tc->hourEnd   && m <= tc->minEnd);
    return afterStart && beforeEnd;
}

static bool evaluateParameterCondition(const ParameterCondition *pc, float value)
{
    switch (pc->op) {
        case OP_LESS_THAN: return value < pc->thresholdMax;
        case OP_MORE_THAN: return value > pc->thresholdMin;
        case OP_BETWEEN:   return (value >= pc->thresholdMin) &&
                                  (value <= pc->thresholdMax);
        default:           return false;
    }
}

static bool evaluateParameterDeltaCondition(const ParameterDeltaCondition *pdc,
                                            float v1, float v2)
{
    float delta = v1 - v2;
    switch (pdc->deltaOp) {
        case OP_LESS_THAN: return delta < pdc->deltaMax;
        case OP_MORE_THAN: return delta > pdc->deltaMin;
        case OP_BETWEEN:   return (delta >= pdc->deltaMin) &&
                                  (delta <= pdc->deltaMax);
        default:           return false;
    }
}

/* Bucket a rule by its conditions so each trigger only touches relevant rules:
 * ENGINE_EVAL_TIME -> rules carrying a COND_TIME (and zero-condition "always"
 * rules); ENGINE_EVAL_NODE -> rules carrying a COND_PARAMETER(_DELTA). A rule
 * with both kinds matches both scopes. */
static bool rule_matches_scope(const AutomationRule *rule, EngineEvalScope scope)
{
    bool has_time = false, has_data = false;
    int c;

    for (c = 0; c < rule->conditionCount; c++) {
        if (rule->conditions[c].conditionType == COND_TIME) {
            has_time = true;
        } else {
            has_data = true;  /* COND_PARAMETER / COND_PARAMETER_DELTA */
        }
    }
    if (scope == ENGINE_EVAL_TIME) {
        return has_time || (rule->conditionCount == 0);
    }
    return has_data;  /* ENGINE_EVAL_NODE */
}

void engine_evaluate(EngineEvalScope scope)
{
    uint8_t a = g_active;
    AutomationRule *rules = g_rules[a];
    uint16_t n = g_count[a];
    uint16_t i;
    int c;

    /* TIME tick runs once per wall-minute. Skip a repeat trigger in the same
     * minute so TIME rules never double-fire. Keyed on the SAME rounded "tick
     * minute" (wall_now_rounded, +2s) that evaluateTimeCondition uses, so the
     * dedup and the COND_TIME range check agree on which minute this tick is -
     * a wake a few ms before :00 maps to the intended minute, not the previous. */
    if (scope == ENGINE_EVAL_TIME) {
        uint8_t h, m;
        if (wall_now_rounded(&h, &m)) {
            int curMin = (int)h * 60 + (int)m;
            if (curMin == g_last_time_min) {
                return;
            }
            g_last_time_min = curMin;
        }
    }

    for (i = 0; i < n; i++) {
        AutomationRule *rule = &rules[i];
        bool allConditionsMet = true;

        if (!rule_matches_scope(rule, scope)) {
            continue;  /* not in this trigger's bucket */
        }

        /* Relay dedup (level-trigger + node-feedback anti-spam): skip if the TARGET
         * node's pump is already in the wanted state. Per-node now (target's own
         * pumpState), so it works for any solar node, not just a global one. */
        if (rule->action.actionType == ACTION_SET_RELAY) {
            const NodeRec *tgt = &g_node[rule->action.nodeAddr];
            uint8_t want = (rule->action.data.value >= 0.5f) ? 1u : 0u;
            if (tgt->type == NODE_SOLAR_CONTROLLER && tgt->d.solar.pumpState == want) {
                continue;
            }
        }

        for (c = 0; c < rule->conditionCount; c++) {
            RuleCondition *rc = &rule->conditions[c];
            bool cond_ok = false;

            switch (rc->conditionType) {
                case COND_TIME:
                    cond_ok = evaluateTimeCondition(&rc->u.time);
                    break;
                case COND_PARAMETER: {
                    ParameterCondition *pc = &rc->u.parameter;
                    /* fail-safe: a node that hasn't reported yet -> condition not met */
                    if (!g_node[pc->nodeAddr].inUse) {
                        cond_ok = false;
                    } else {
                        float val = getNodeParam(pc->nodeAddr, pc->parameter);
                        cond_ok = evaluateParameterCondition(pc, val);
                    }
                    break;
                }
                case COND_PARAMETER_DELTA: {
                    ParameterDeltaCondition *pdc = &rc->u.parameterDelta;
                    if (!g_node[pdc->nodeAddr1].inUse || !g_node[pdc->nodeAddr2].inUse) {
                        cond_ok = false;
                    } else {
                        float v1 = getNodeParam(pdc->nodeAddr1, pdc->parameter1);
                        float v2 = getNodeParam(pdc->nodeAddr2, pdc->parameter2);
                        cond_ok = evaluateParameterDeltaCondition(pdc, v1, v2);
                    }
                    break;
                }
                default:
                    cond_ok = false;
                    break;
            }

            if (!cond_ok) {
                allConditionsMet = false;
                break;  /* AND: one failed => rule not met */
            }
        }

        if (!allConditionsMet) {
            continue;
        }

        /* All conditions met -> build the action. Node actions route to the target
         * address (msg.id = nodeAddr, msg.type = that node's actual type); the sink
         * sends msg to the node ONLY when nodeAddr != 0 (see drainEngineOutbox), so
         * SEND_MESSAGE (nodeAddr 0, system notification) reports RULE_FIRED without a
         * bogus RF send. `value` is a float (0/1, %, ...); dispatch per actionType. */
        MessageStruct msg;
        memset(&msg, 0, sizeof(msg));
        msg.id   = rule->action.nodeAddr;
        msg.type = g_node[rule->action.nodeAddr].type;

        if (rule->action.actionType == ACTION_SET_RELAY) {
            msg.cmd = CMD_TURN_PUMP_ON_OFF;
            msg.payload.pumpData.pumpState =
                (rule->action.data.value >= 0.5f) ? 1u : 0u;
            msg.length = (uint8_t)(sizeof(msg.payload.pumpData) + 4u);
        } else if (rule->action.actionType == ACTION_SEND_MESSAGE) {
            msg.cmd = CMD_SEND_TEXT_MSG;
            strncpy(msg.payload.textData.text,
                    rule->action.data.message,
                    sizeof(msg.payload.textData.text) - 1);
            msg.payload.textData.text[sizeof(msg.payload.textData.text) - 1] = '\0';
            msg.length = (uint8_t)(4u + strlen(msg.payload.textData.text) + 1u);
        } else {
            continue;  /* unknown action type */
        }

        if (g_action_fn != NULL) {
            g_action_fn(&msg, i, &rule->action, g_action_ctx);
        }
    }
}

/* ========================================================================= *
 * RULESET UPLOAD - atomic swap
 * ========================================================================= */
bool engine_rules_begin(uint16_t count)
{
    if (count > MAX_RULES) {
        return false;
    }
    g_shadow = (uint8_t)(g_active ^ 1u);
    g_shadow_expected = count;
    g_shadow_filled = 0;
    g_building = true;
    return true;
}

bool engine_rules_item(uint16_t index, const AutomationRule *rule)
{
    if (!g_building || rule == NULL) {
        return false;
    }
    if (index >= g_shadow_expected) {
        return false;
    }
    memcpy(&g_rules[g_shadow][index], rule, sizeof(AutomationRule));
    g_shadow_filled++;
    return true;
}

bool engine_rules_commit(uint16_t expectedCount, uint32_t crc32)
{
    uint32_t calc;

    if (!g_building) {
        return false;
    }
    g_building = false;  /* this attempt is now resolved either way */

    if (expectedCount != g_shadow_expected ||
        g_shadow_filled != expectedCount) {
        return false;  /* count mismatch -> keep active set */
    }

    calc = crc32_calc((const uint8_t *)g_rules[g_shadow],
                      (size_t)expectedCount * sizeof(AutomationRule));
    if (calc != crc32) {
        return false;  /* corrupt -> keep active set */
    }

    g_count[g_shadow] = expectedCount;
    g_active = g_shadow;  /* atomic swap */
    g_last_time_min = -1; /* new ruleset: allow a fresh TIME evaluation */
    return true;
}

uint16_t engine_rules_active_count(void)
{
    return g_count[g_active];
}
